Skidlz/Pearl-Drum-X-MIDI-retrofit/src/midi.c

#include <stddef.h>
#include "midi.h"
#include "uart.h"

uint8_t midi_chan = 0xff; //MIDI channel

void set_MIDI_key_press(void (*ptr)(uint8_t, uint8_t)) { MIDI_key_press = ptr; }
void set_MIDI_key_release(void (*ptr)(uint8_t)) { MIDI_key_release = ptr; }
void set_song_pos_ptr(void (*ptr)(int)) { song_pos_ptr = ptr; }
void set_rt_clock(void (*ptr)()) { rt_clock = ptr; }
void set_rt_start(void (*ptr)()) { rt_start = ptr; }
void set_rt_cont(void (*ptr)()) { rt_cont = ptr; }
void set_rt_stop(void (*ptr)()) { rt_stop = ptr; }
void set_cntrl_chng(void (*ptr)(uint8_t, uint8_t)) { cntrl_chng = ptr; }
void set_prg_chng(void (*ptr)(uint8_t)) { prg_chng = ptr; }
void set_MIDI_pitch_bend(void (*ptr)(int)) { MIDI_pitch_bend = ptr; }

uint8_t handle_com(uint8_t com, uint8_t arg_cnt, uint8_t *args) {
    switch (com & 0xf0) {
        case 0x90: { //key press
            if (arg_cnt < 2) return arg_cnt;

            uint8_t note = args[0];
            uint8_t vel = args[1];
            if (vel > 0) { //on
                if (MIDI_key_press != NULL) MIDI_key_press(note, vel);
            } else if (MIDI_key_release != NULL) { //off
                MIDI_key_release(note);
            }
            return 0; //zero args remain
        }
        case 0x80: { //key release
            if (arg_cnt < 2) return arg_cnt;

            uint8_t note = args[0];
            if (MIDI_key_release != NULL)MIDI_key_release(note);
            return 0;
        }
        case 0xb0: {//control
            if (arg_cnt < 2) return arg_cnt;

            uint8_t con = args[0];
            uint8_t val = args[1];
            if (cntrl_chng != NULL)cntrl_chng(con, val);
            return 0;
        }
        case 0xe0: { //pitch bend
            if (arg_cnt < 2) return arg_cnt;

            int value = args[0] | (args[1] << 7); //msb
            if (MIDI_pitch_bend != NULL)MIDI_pitch_bend(value);
            return 0;
        }
        case 0xa0: //Polyphonic Key Pressure (Aftertouch)
            if (arg_cnt < 2) return arg_cnt;
            return 0;
        case 0xc0: //Program Change
            if (arg_cnt < 1) return arg_cnt;

            if (prg_chng != NULL)prg_chng(args[0]);
            return 0;
        case 0xd0: //Channel Pressure
            if (arg_cnt < 1) return arg_cnt;
            return 0;
        default: //error
            return arg_cnt;
    }
}

uint8_t handle_glob_com(uint8_t com, uint8_t arg_cnt, uint8_t *args) {
    switch (com) {
        case 0xf0: //SysEx
            return 1;
        case 0xf2: //Song Position Pointer
            if (arg_cnt < 2)return arg_cnt;
            unsigned int pos = args[0] | (args[1] << 7);
            if (song_pos_ptr != NULL)song_pos_ptr(pos);
            return 0;
        case 0xf1: //MIDI Time Code Quarter Frame
        case 0xf3: //Song Select
            if (arg_cnt < 1)return arg_cnt;
            return 0;
        case 0xf7: //SysEx off
            break;
        case 0xf6: //Tune Request
        default: //Undefined
            return 0;
    }

    return 0; //shut up compiler warnings
}

uint8_t skip_com(uint8_t com, uint8_t arg_cnt, uint8_t *args) {
    switch (com & 0xf0) {
        case 0x90: //key press
        case 0x80: //key release
        case 0xb0: //control
        case 0xe0: //pitch bend
        case 0xa0: //Polyphonic Key Pressure (Aftertouch)
            if (arg_cnt < 2) return arg_cnt;
            return 0;
        case 0xc0: //Program Change
        case 0xd0: //Channel Pressure
            if (arg_cnt < 1) return arg_cnt;
            return 0;
        default:
            return 0;
    }
}

void handle_midi() {
    static uint8_t last_com = 0x90;
    static uint8_t arg_cnt = 0;
    static uint8_t args[2];
    const int arg_max = 2;

    //function returns remaining args
    uint8_t loop_temp = uart_get();
    if (loop_temp >= 0xf8) {
        handle_realtime(loop_temp);
    } else {
        if (loop_temp & 0x80) { //command
            last_com = loop_temp;
            arg_cnt = 0;
        } else if (arg_cnt < arg_max) {
            args[arg_cnt++] = loop_temp;
        }

        if (last_com >= 0xf0) {
            arg_cnt = handle_glob_com(last_com, arg_cnt, args); //no channel
        } else {
            if (midi_chan == 0xff) midi_chan = last_com & 0x0f; //define our chan?
            if ((last_com & 0x0f) == midi_chan) arg_cnt = handle_com(last_com, arg_cnt, args); //right chan
            else arg_cnt = skip_com(last_com, arg_cnt, args); //wrong channel
        }
    }
}

void handle_realtime(uint8_t mess) {
    switch (mess) {
        case 0xf8: //Timing Clock
            if (rt_clock != NULL)rt_clock();
            break;
        case 0xfA: //Start Sequence
            if (rt_start != NULL)rt_start();
            break;
        case 0xfB: //Continue Sequence
            if (rt_cont != NULL)rt_cont();
            break;
        case 0xfC: //Stop Sequence
            if (rt_stop != NULL)rt_stop();
            break;
    }
}
