Skidlz/Pearl-Drum-X-MIDI-retrofit/src/uart.h

#include <stdint.h>
void uart_init(long);		/* Initialize UART and Flush FIFOs */
uint8_t uart_get (void);	/* Get a byte from UART Rx FIFO */
uint8_t uart_test(void);	/* Check number of data in UART Rx FIFO */
